Enali69Enali/Station_Meteo_23-24/rapport_de_séance/Rapport22_12_2023PELLETIER.pdf

# Rapport de séance n°6

Séance du 22/12/2023

## Objectif de la séance : Réalisation des modèles 3D

Modéliser la fente sur la boite de la girouette et finaliser les modélisation

## Réalisé pendant la séance

Lors de cette séance, sans ma camarade ou mon professeur je n’ai pas pu beaucoup avancé. J’ai seulement pu finaliser la boite et le couvercle en modélisation. En y ajoutant une fente pour maintenir la carte dedans.

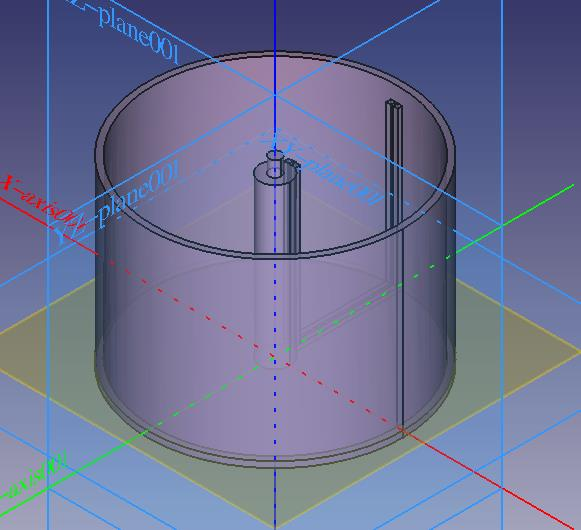
[picture p33: figure]

## Problèmes de la séance

Malheureusement sans la carte ni le masque pour appliquer la pate pour mettre les résistances, les tests n’étaient pas possible.

## A faire attention

## A faire à la prochaine séance

Tester notre PCB.
