Enali69Enali/Station_Meteo_23-24/rapport_de_séance/Rapport04_12_2023DUEEMOREAU.pdf

[230-

on mesure | Vout=3 , | 258V | lorsque le phototransistor

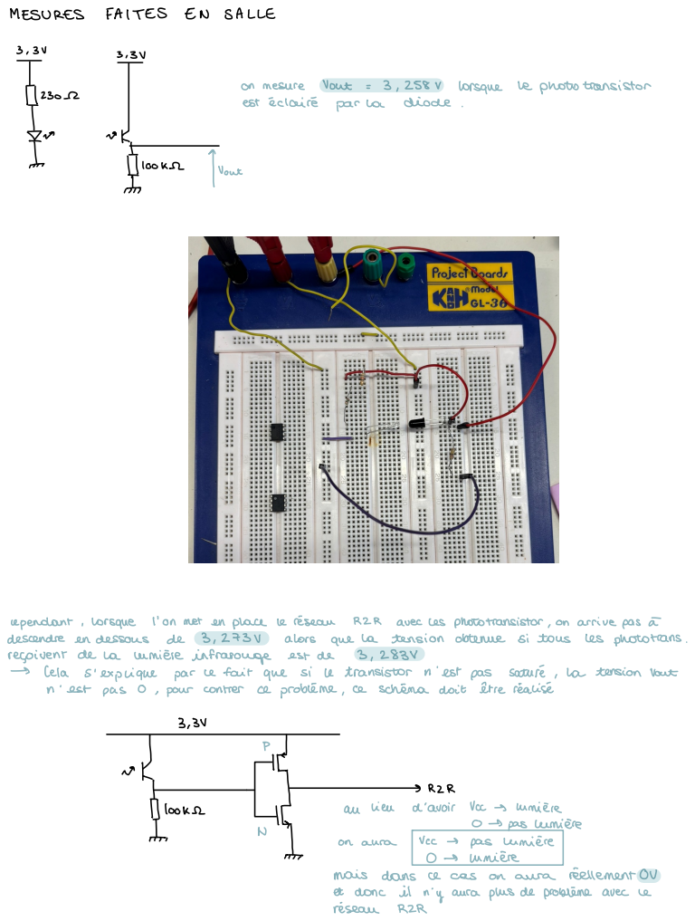
[picture p42: page 1]
MESURES; FAITES; SALLE; est éclairé; par la; diode; #I looke You; rependant ,; lorsque; l'on met en place le réseau; avec les phototransistor ,; arrive pas à; descendre en dessous; alors; que la; tension obtenue; si tous; les phototrans.; reçoivent de la; lumière infrarouge est de; Cela; s'explique par le fait que si le transistor n'est pas; saturé ,; la tension Vout; n'est; pas 0 ,; pour contrer; problème ,le; schema doit; être réalisé; # wit; C RZR; ↓ looks; lieu; d'avoir; lunière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
