Enali69Enali/Station_Meteo_23-24/Travail_bonus/projet_lora_emetteur.ino

#include <SPI.h>
#include <LoRa.h>

#define ss 18
#define rst 14
#define dio0 26

int counter = 0;

void setup() {
  Serial.begin(9600);
  delay(100);
  while (!Serial);

  Serial.println("LoRa Sender");
  SPI.begin();
  LoRa.setPins(ss,rst,dio0);
  if (!LoRa.begin(868E6)) {
    Serial.println("Starting LoRa failed!");
    while (1);
  }
}

void loop() {
  Serial.print("Sending packet: ");
  Serial.println(counter);

  // send packet
  LoRa.beginPacket();
  LoRa.print("hello ");
  LoRa.print(counter);
  LoRa.endPacket();

  counter++;

  delay(5000);
}
